dannygrob/OpenWatch/Software/largefont.c

/*
 * largefont.c
 *
 *  Created on: 28 Sep 2019
 *      Author: Nitwit
 */
#include "displayDriver.h"
#include "largefont.h"
#include "imageOffsets.h"

int displayGetWidthClockCharacter(char CHARACTER) {
        int letterWidth = 0;
        switch(CHARACTER)
        {
            case '1':

                    letterWidth = 14;
                    break;

            case '2':

                    letterWidth = 23;
                    break;
            case '3':

                    letterWidth = 24;
                    break;

            case '4':

                    letterWidth = 24;
                    break;
            case '5':

                    letterWidth = 24;
                    break;

            case '6':

                    letterWidth = 23;
                    break;
            case '7':

                    letterWidth = 22;
                    break;

            case '8':

                    letterWidth = 24;
                    break;
            case '9':

                    letterWidth = 25;
                    break;

            case '0':

                    letterWidth = 24;
                    break;
            case ':':
                    letterWidth = 5;
                    break;

        }

        return letterWidth;

}

int displayDrawClockNumber(int X_START, int Y_START, char CHARACTER) {

        int letterWidth = displayGetWidthClockCharacter(CHARACTER);
        int row = 0;
        int column = 0;

        switch(CHARACTER)
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
                    row = 2;
                    break;

            case '0':
                    column = 1;
                    row = 1;
                    break;
            case ':':
                    column = 1;
                    row = 3;
                    break;

        }
        if (bold == 1) {
                displayPartialImageFromMemory(X_START,Y_START,(column - 1) * NUMBER_FONT_CHARACTER_WIDTH , (row - 1) * NUMBER_FONT_CHARACTER_HEIGHT,NUMBER_FONT_CHARACTER_WIDTH,NUMBER_FONT_CHARACTER_HEIGHT,MEDIUMFONT_OFFSET);
        } else {
                displayPartialImageFromMemory(X_START,Y_START,(column - 1) * NUMBER_FONT_CHARACTER_WIDTH , (row - 1) * NUMBER_FONT_CHARACTER_HEIGHT,NUMBER_FONT_CHARACTER_WIDTH,NUMBER_FONT_CHARACTER_HEIGHT,LIGHTFONT_OFFSET);
        }
        return letterWidth;

}
